Markahofmeister/sinking-clock/electrical/SPICE/AC-adapter-transient-analysis.asc

C1: cap; 100µ
C2: cap; 10µ
L1: ind; 25µ; Rser=1
R1: res; 10k
R2: res; 1
S1: sw; 5
V1: voltage; 12
V2: voltage; PULSE(0 5 2m 1n 1n 2m)
Named nets: 0
.tran 3.5m
.model MYSW SW(Ron=0.01 Roff=1Meg Vt=4 Vh=0)
