Markahofmeister/sinking-clock/electrical/SPICE/Draft1.asc

C1: cap; 0.1µ
R1: res; 1Meg
R2: res; 1k
R3: res; 40k
S1: sw; 5
V1: voltage; 3.3
V2: voltage; PULSE(0 5 10m 1n 1n 50m)
V3: voltage; {3.3*0.7}
Named nets: 0, vin, vout, vHIGH
.model MYSW SW(Ron=0.01 Roff = 1Meg Vt=4 Vh=0)
.tran 100m
